alangecker/sick-spider/output/0.1-prototype/spider2-assembly.pdf

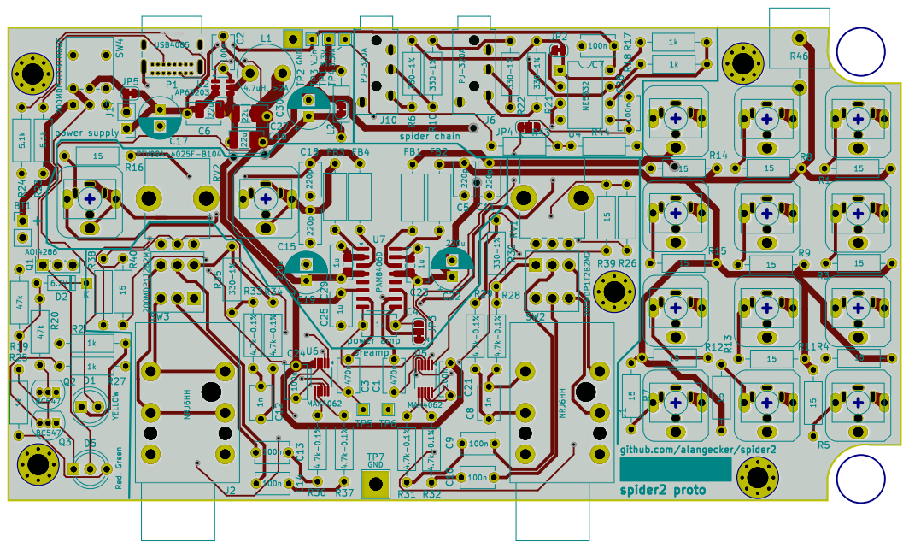
[picture p40: page 1]

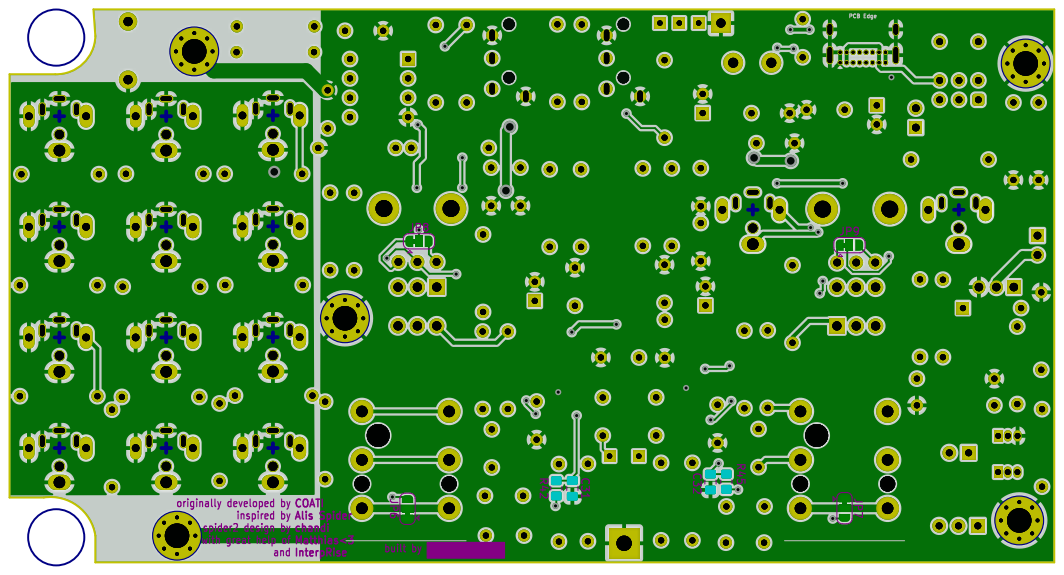
[picture p41: page 2]

inspired by
spider2 design by
with great help of

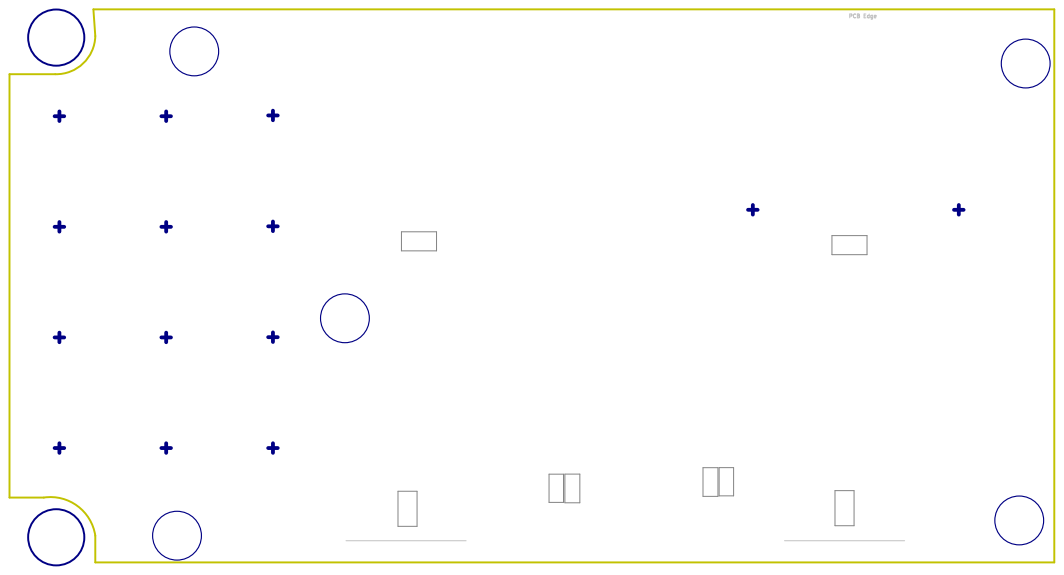
[picture p42: page 3]
Title:; File: spider2.kicad_pcb; Sheet:; Bottom courtyard; area; PCB Edge

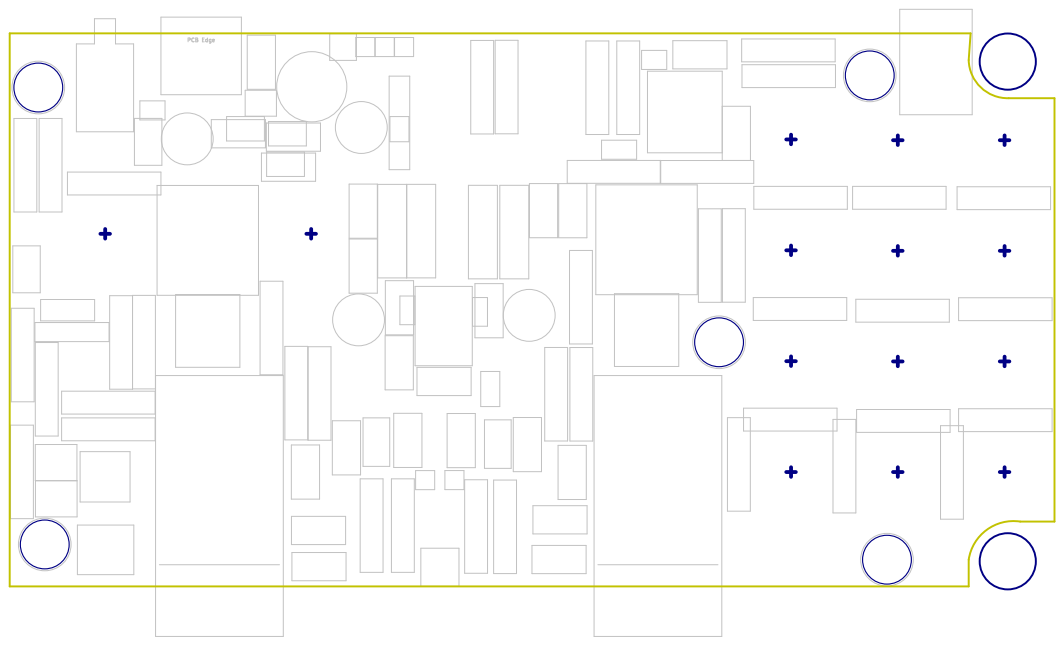
[picture p43: page 4]
Title:; File: spider2.kicad_pcb; Sheet:; Front courtyard area; PCB Edge

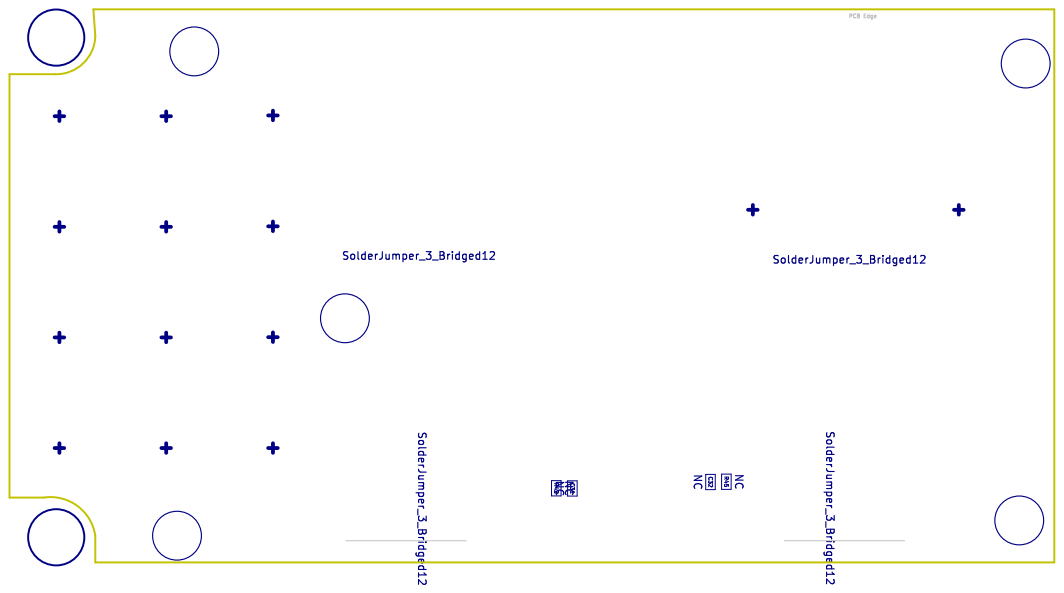
[picture p44: page 5]
Title:; File: spider2.kicad_pcb; Sheet:; Bottom documentation; PCB Edge; SolderJumper_3_Bridged12; SolderJumper_3_Bridged12 SolderJumper_3_Bridged12

# TP4TP1 C20

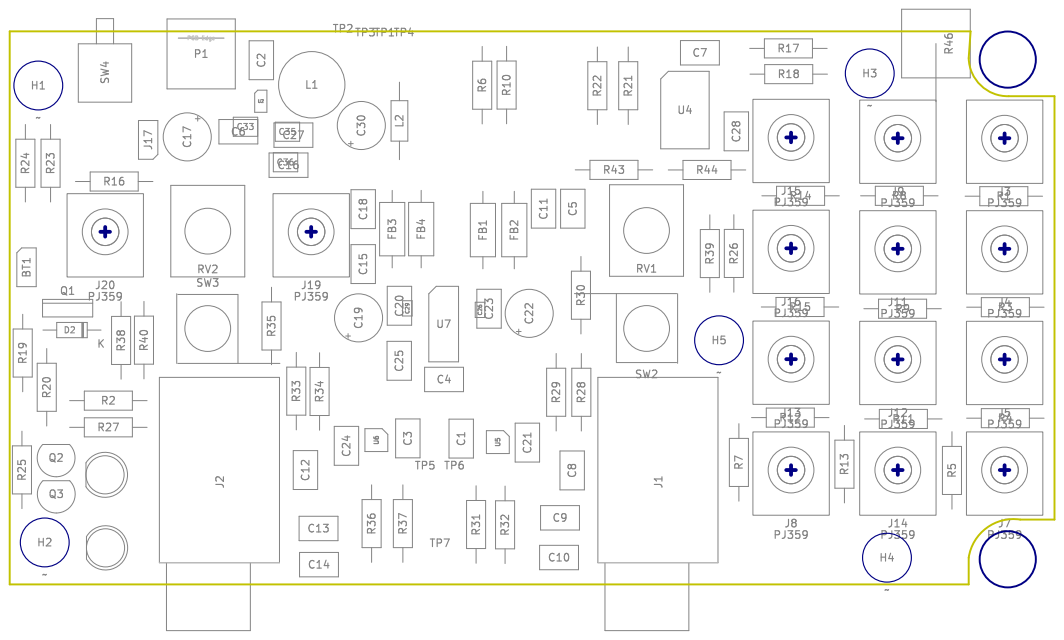
[picture p45: page 6]
