alangecker/sick-spider/output/0.1-prototype/spider2-schematic.pdf

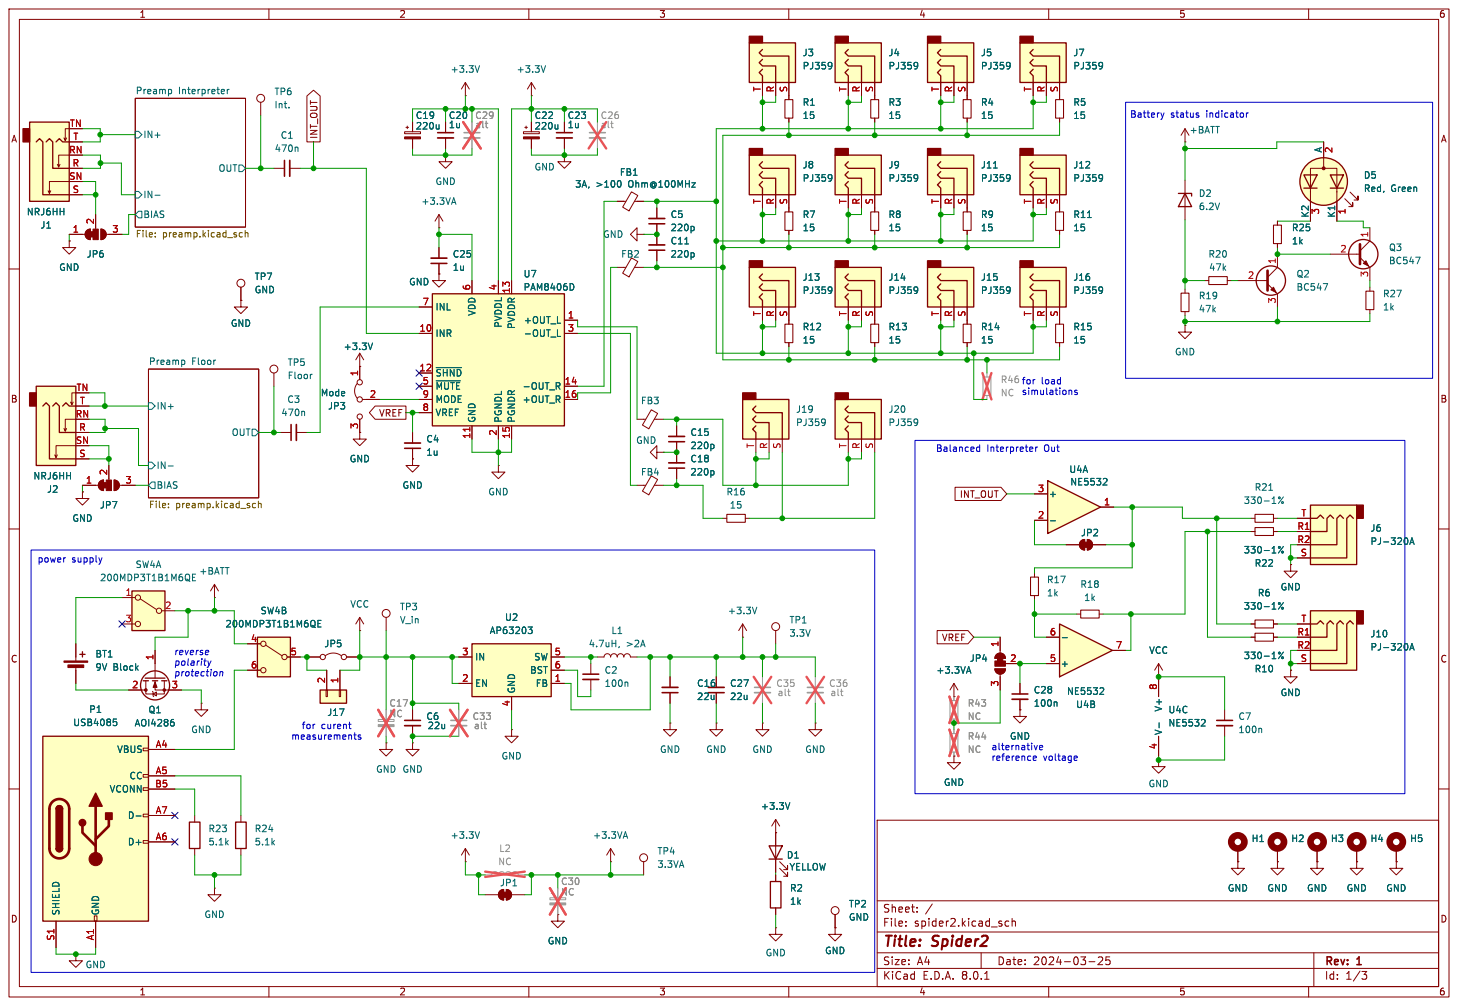
[picture p46: page 1]

Preamp Interpreter File: preamp.kicad_sch

4 SW 5 BST 6 C17 NC GND GND

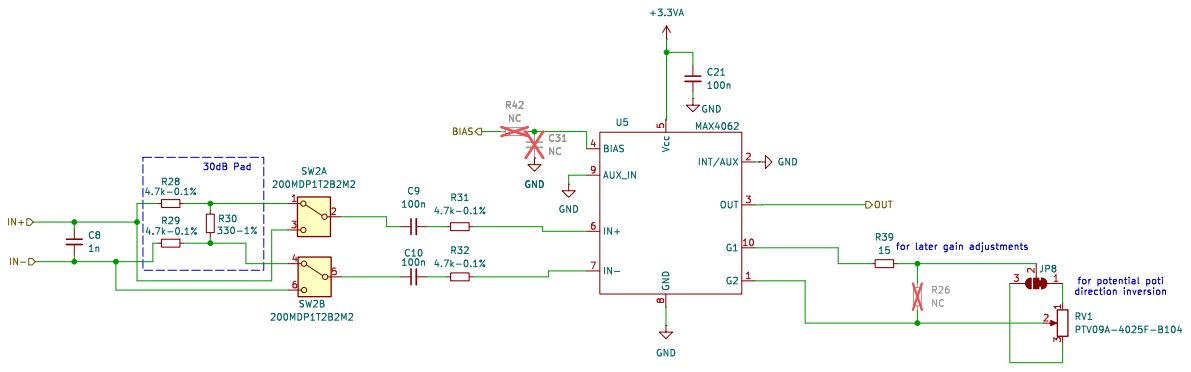
[picture p47: page 2]

for later gain adjustments

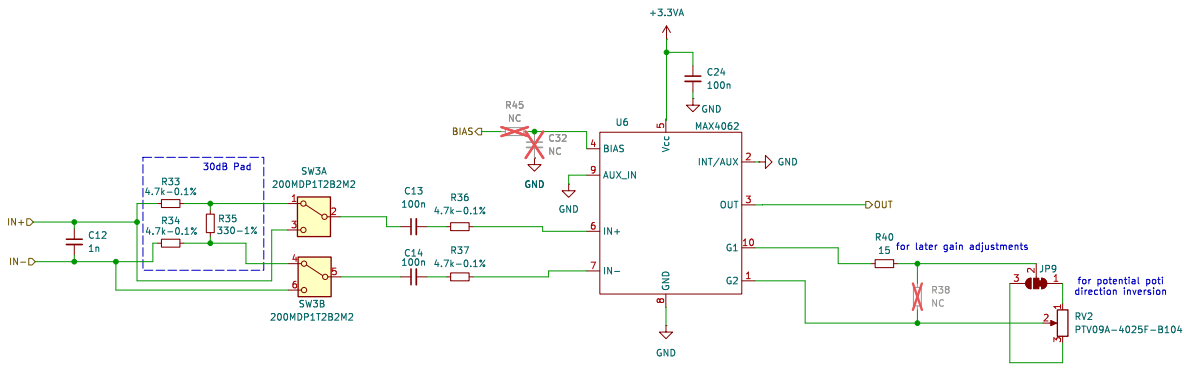
[picture p48: page 3]

for later gain adjustments
